menbou0202/Nape/doc/images/DSCF0460.jpeg

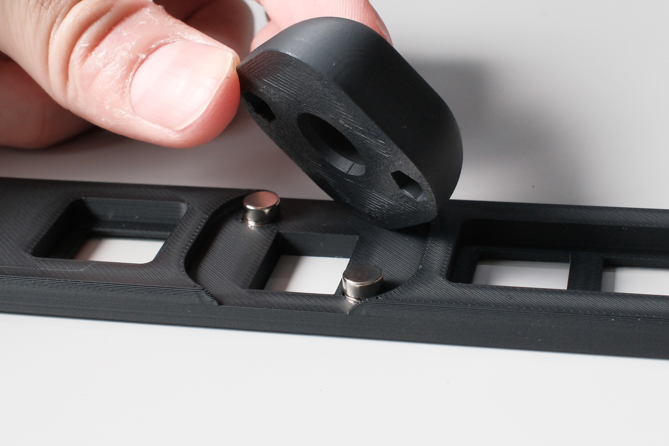
doc/images/DSCF0460.jpeg
