menbou0202/Nape/doc/images/DSCF0480.jpeg

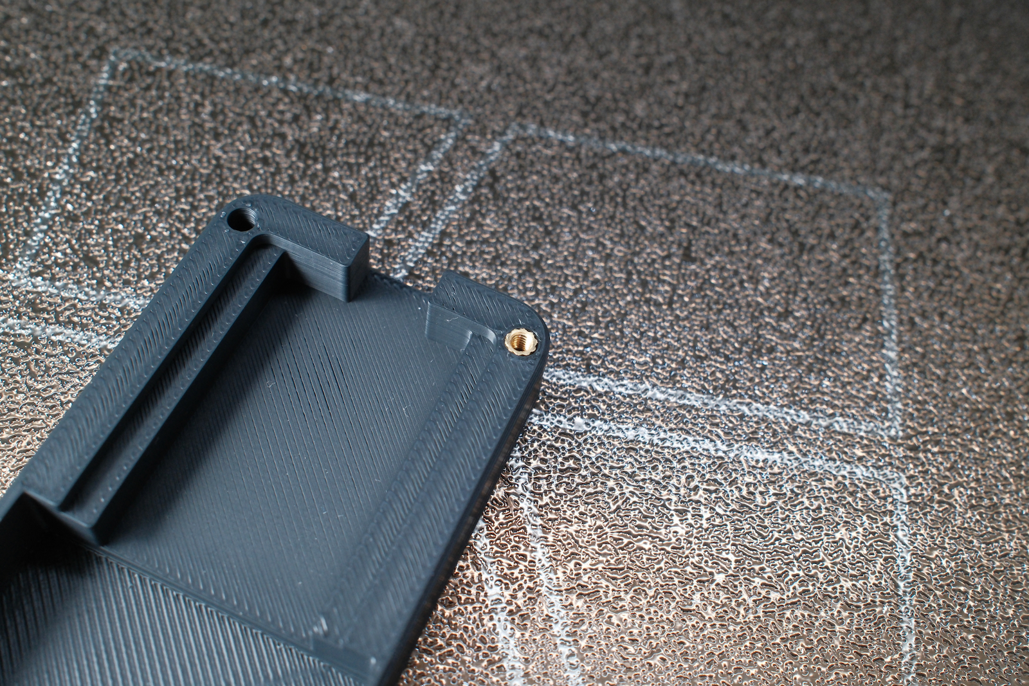
doc/images/DSCF0480.jpeg
