menbou0202/Nape/doc/images/list5.jpeg

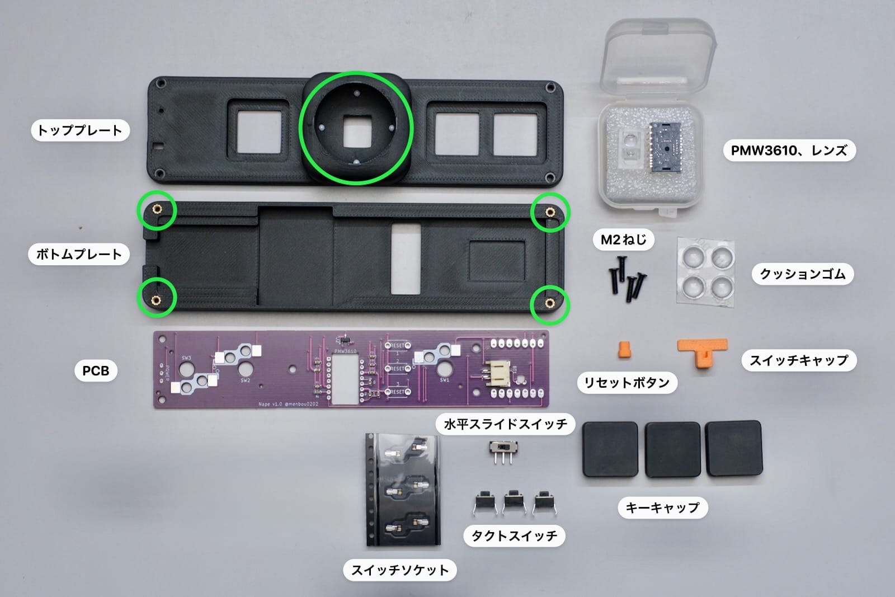
doc/images/list5.jpeg
