menbou0202/Nape/doc/images/Nape_1.jpeg

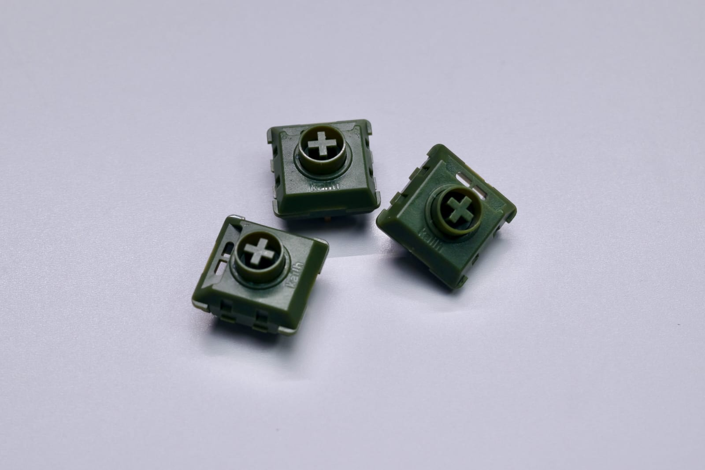
doc/images/Nape_1.jpeg
