menbou0202/Nape/doc/images/NapeBuildGuide_00003_mod-1.jpeg

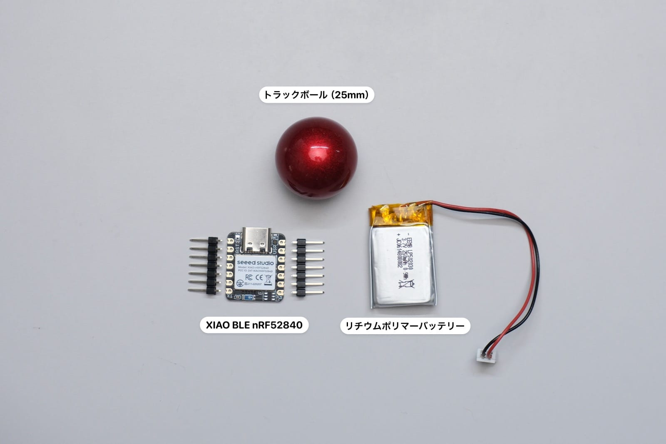
doc/images/NapeBuildGuide_00003_mod-1.jpeg
